RicardoSung/Apple_Sugar_Detector/PCB/v3/FPGA_CCD/allegro/test.png

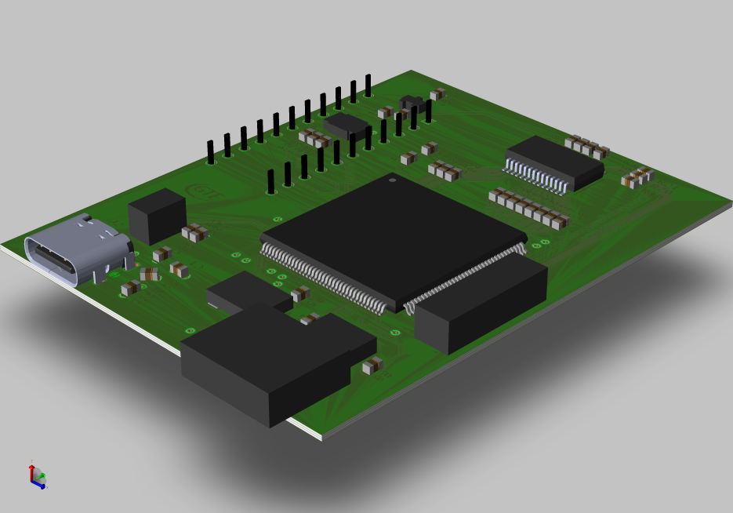
PCB/v3/FPGA_CCD/allegro/test.png
