RicardoSung/Apple_Sugar_Detector/Verilog/v1/UART.v

`timescale 1ns / 1ps
//////////////////////////////////////////////////////////////////////////////////
// Company: 
// Engineer: 
// 
// Create Date:    12:24:14 06/28/2021 
// Design Name: 
// Module Name:    UART 
// Project Name: 
// Target Devices: 
// Tool versions: 
// Description: 
//
// Dependencies: 
//
// Revision: 
// Revision 0.01 - File Created
// Additional Comments: 
//
//////////////////////////////////////////////////////////////////////////////////
module UART(
    );


endmodule
