RicardoSung/Apple_Sugar_Detector/Android Application/usbSerialExamples/src/main/java/com/hoho/android/usbserial/examples/TerminalFragment.java

package com.hoho.android.usbserial.examples;

import android.app.PendingIntent;
import android.content.BroadcastReceiver;
import android.content.Context;
import android.content.Intent;
import android.content.IntentFilter;
import android.graphics.Color;
import android.hardware.usb.UsbDevice;
import android.hardware.usb.UsbDeviceConnection;
import android.hardware.usb.UsbManager;
import android.os.Build;
import android.os.Bundle;
import android.os.Handler;
import android.os.Looper;
import android.text.Spannable;
import android.text.SpannableStringBuilder;
import android.text.TextUtils;
import android.text.method.ScrollingMovementMethod;
import android.text.style.ForegroundColorSpan;
import android.util.Log;
import android.view.LayoutInflater;
import android.view.Menu;
import android.view.MenuInflater;
import android.view.MenuItem;
import android.view.MotionEvent;
import android.view.View;
import android.view.ViewGroup;
import android.widget.TextView;
import android.widget.Toast;
import android.widget.ToggleButton;

import androidx.annotation.NonNull;
import androidx.annotation.Nullable;
import androidx.annotation.RequiresApi;
import androidx.fragment.app.Fragment;

import com.hoho.android.usbserial.driver.UsbSerialDriver;
import com.hoho.android.usbserial.driver.UsbSerialPort;
import com.hoho.android.usbserial.driver.UsbSerialProber;
import com.hoho.android.usbserial.util.HexDump;
import com.hoho.android.usbserial.util.SerialInputOutputManager;

import com.github.mikephil.charting.animation.Easing;
import com.github.mikephil.charting.charts.LineChart;

import com.github.mikephil.charting.components.Legend;
import com.github.mikephil.charting.components.Legend.LegendForm;
import com.github.mikephil.charting.components.LimitLine;
import com.github.mikephil.charting.components.LimitLine.LimitLabelPosition;
import com.github.mikephil.charting.components.XAxis;
import com.github.mikephil.charting.components.YAxis;
import com.github.mikephil.charting.data.Entry;
import com.github.mikephil.charting.data.LineData;
import com.github.mikephil.charting.data.LineDataSet;
import com.github.mikephil.charting.highlight.Highlight;
import com.github.mikephil.charting.interfaces.datasets.ILineDataSet;
import com.github.mikephil.charting.listener.ChartTouchListener;
import com.github.mikephil.charting.listener.OnChartGestureListener;
import com.github.mikephil.charting.listener.OnChartValueSelectedListener;
import com.github.mikephil.charting.utils.Utils;

import java.io.BufferedReader;
import java.io.IOException;
import java.io.InputStream;
import java.io.InputStreamReader;
import java.io.UnsupportedEncodingException;
import java.util.ArrayList;
import java.util.Arrays;
import java.util.EnumSet;

public class TerminalFragment extends Fragment implements SerialInputOutputManager.Listener, OnChartGestureListener, OnChartValueSelectedListener {

    @Override
    public void onChartGestureStart(MotionEvent me, ChartTouchListener.ChartGesture lastPerformedGesture) {
        Log.i("Gesture", "START, x: " + me.getX() + ", y: " + me.getY());
    }

    @Override
    public void onChartGestureEnd(MotionEvent me, ChartTouchListener.ChartGesture lastPerformedGesture) {
        Log.i("Gesture", "END, lastGesture: " + lastPerformedGesture);

        // un-highlight values after the gesture is finished and no single-tap
        if(lastPerformedGesture != ChartTouchListener.ChartGesture.SINGLE_TAP)
            mChart.highlightValues(null); // or highlightTouch(null) for callback to onNothingSelected(...)
    }

    @Override
    public void onChartLongPressed(MotionEvent me) {
        Log.i("LongPress", "Chart longpressed.");
    }

    @Override
    public void onChartDoubleTapped(MotionEvent me) {
        Log.i("DoubleTap", "Chart double-tapped.");
    }

    @Override
    public void onChartSingleTapped(MotionEvent me) {
        Log.i("SingleTap", "Chart single-tapped.");
    }

    @Override
    public void onChartFling(MotionEvent me1, MotionEvent me2, float velocityX, float velocityY) {
        Log.i("Fling", "Chart flinged. VeloX: " + velocityX + ", VeloY: " + velocityY);
    }

    @Override
    public void onChartScale(MotionEvent me, float scaleX, float scaleY) {
        Log.i("Scale / Zoom", "ScaleX: " + scaleX + ", ScaleY: " + scaleY);
    }

    @Override
    public void onChartTranslate(MotionEvent me, float dX, float dY) {
        Log.i("Translate / Move", "dX: " + dX + ", dY: " + dY);
    }

    @Override
    public void onValueSelected(Entry e, Highlight h) {
        Log.i("Entry selected", e.toString());
        Log.i("LOWHIGH", "low: " + mChart.getLowestVisibleX() + ", high: " + mChart.getHighestVisibleX());
        Log.i("MIN MAX", "xmin: " + mChart.getXChartMin() + ", xmax: " + mChart.getXChartMax() + ", ymin: " + mChart.getYChartMin() + ", ymax: " + mChart.getYChartMax());
    }

    @Override
    public void onNothingSelected() {
        Log.i("Nothing selected", "Nothing selected.");
    }

    private enum UsbPermission { Unknown, Requested, Granted, Denied }

    private static final String INTENT_ACTION_GRANT_USB = BuildConfig.APPLICATION_ID + ".GRANT_USB";
    private static final int WRITE_WAIT_MILLIS = 2000;
    private static final int READ_WAIT_MILLIS = 2000;

    private int deviceId, portNum, baudRate;
    private boolean withIoManager;

    private final BroadcastReceiver broadcastReceiver;
    private final Handler mainLooper;
    private TextView receiveText;
    private ControlLines controlLines;

    private SerialInputOutputManager usbIoManager;
    private UsbSerialPort usbSerialPort;
    private UsbPermission usbPermission = UsbPermission.Unknown;
    private boolean connected = false;

    private LineChart mChart;
    private TextView tvX, tvY;

    public TerminalFragment() {
        broadcastReceiver = new BroadcastReceiver() {
            @Override
            public void onReceive(Context context, Intent intent) {
                if(INTENT_ACTION_GRANT_USB.equals(intent.getAction())) {
                    usbPermission = intent.getBooleanExtra(UsbManager.EXTRA_PERMISSION_GRANTED, false)
                            ? UsbPermission.Granted : UsbPermission.Denied;
                    connect();
                }
            }
        };
        mainLooper = new Handler(Looper.getMainLooper());
    }

    /*
     * Lifecycle
     */
    @Override
    public void onCreate(@Nullable Bundle savedInstanceState) {
        super.onCreate(savedInstanceState);
        setHasOptionsMenu(true);
        setRetainInstance(true);
        deviceId = getArguments().getInt("device");
        portNum = getArguments().getInt("port");
        baudRate = getArguments().getInt("baud");
        withIoManager = getArguments().getBoolean("withIoManager");
    }

    @Override
    public void onResume() {
        super.onResume();
        getActivity().registerReceiver(broadcastReceiver, new IntentFilter(INTENT_ACTION_GRANT_USB));

        if(usbPermission == UsbPermission.Unknown || usbPermission == UsbPermission.Granted)
            mainLooper.post(this::connect);
    }

    @Override
    public void onPause() {
        if(connected) {
            status("disconnected");
            disconnect();
        }
        getActivity().unregisterReceiver(broadcastReceiver);
        super.onPause();
    }

    /*
     * UI
     */
    @Override
    public View onCreateView(@NonNull LayoutInflater inflater, ViewGroup container, Bundle savedInstanceState) {
        View view = inflater.inflate(R.layout.fragment_terminal, container, false);
        receiveText = view.findViewById(R.id.receive_text);                          // TextView performance decreases with number of spans
        receiveText.setTextColor(getResources().getColor(R.color.colorRecieveText)); // set as default color to reduce number of spans
        receiveText.setMovementMethod(ScrollingMovementMethod.getInstance());
        TextView sendText = view.findViewById(R.id.send_text);
        View sendBtn = view.findViewById(R.id.send_btn);
        sendBtn.setOnClickListener(v -> send(sendText.getText().toString()));
        View receiveBtn = view.findViewById(R.id.receive_btn);
        View displayBtn = view.findViewById(R.id.display);
        View calculateBtn = view.findViewById(R.id.calculate);
        mChart = (LineChart) view.findViewById(R.id.lineChart);
        controlLines = new ControlLines(view);
        initLineChart();
        displayBtn.setOnClickListener(v -> displayChart());
        calculateBtn.setOnClickListener(v -> calculate());
        if(withIoManager) {
            receiveBtn.setVisibility(View.GONE);
        } else {
            receiveBtn.setOnClickListener(v -> read());
        }
        return view;
    }

    @Override
    public void onCreateOptionsMenu(@NonNull Menu menu, MenuInflater inflater) {
        inflater.inflate(R.menu.menu_terminal, menu);
    }

    @Override
    public boolean onOptionsItemSelected(MenuItem item) {
        int id = item.getItemId();
        if (id == R.id.clear) {
            receiveText.setText("");
            receiveText.setText(String.valueOf(baudRate));
            return true;
        } else if( id == R.id.send_break) {
            if(!connected) {
                Toast.makeText(getActivity(), "not connected", Toast.LENGTH_SHORT).show();
            } else {
                try {
                    usbSerialPort.setBreak(true);
                    Thread.sleep(100); // should show progress bar instead of blocking UI thread
                    usbSerialPort.setBreak(false);
                    SpannableStringBuilder spn = new SpannableStringBuilder();
                    spn.append("send <break>\n");
                    spn.setSpan(new ForegroundColorSpan(getResources().getColor(R.color.colorSendText)), 0, spn.length(), Spannable.SPAN_EXCLUSIVE_EXCLUSIVE);
                    receiveText.append(spn);
                } catch(UnsupportedOperationException ignored) {
                    Toast.makeText(getActivity(), "BREAK not supported", Toast.LENGTH_SHORT).show();
                } catch(Exception e) {
                    Toast.makeText(getActivity(), "BREAK failed: " + e.getMessage(), Toast.LENGTH_SHORT).show();
                }
            }
            return true;
        } else {
            return super.onOptionsItemSelected(item);
        }
    }

    /*
     * Serial
     */
    @Override
    public void onNewData(byte[] data) {
        mainLooper.post(() -> {
            receive(data);
        });
    }

    @Override
    public void onRunError(Exception e) {
        mainLooper.post(() -> {
            status("connection lost: " + e.getMessage());
            disconnect();
        });
    }

    /*
     * Serial + UI
     */
    private void connect() {
        UsbDevice device = null;
        UsbManager usbManager = (UsbManager) getActivity().getSystemService(Context.USB_SERVICE);
        for(UsbDevice v : usbManager.getDeviceList().values())
            if(v.getDeviceId() == deviceId)
                device = v;
        if(device == null) {
            status("connection failed: device not found");
            return;
        }
        UsbSerialDriver driver = UsbSerialProber.getDefaultProber().probeDevice(device);
        if(driver == null) {
            driver = CustomProber.getCustomProber().probeDevice(device);
        }
        if(driver == null) {
            status("connection failed: no driver for device");
            return;
        }
        if(driver.getPorts().size() < portNum) {
            status("connection failed: not enough ports at device");
            return;
        }
        usbSerialPort = driver.getPorts().get(portNum);
        UsbDeviceConnection usbConnection = usbManager.openDevice(driver.getDevice());
        if(usbConnection == null && usbPermission == UsbPermission.Unknown && !usbManager.hasPermission(driver.getDevice())) {
            usbPermission = UsbPermission.Requested;
            PendingIntent usbPermissionIntent = PendingIntent.getBroadcast(getActivity(), 0, new Intent(INTENT_ACTION_GRANT_USB), 0);
            usbManager.requestPermission(driver.getDevice(), usbPermissionIntent);
            return;
        }
        if(usbConnection == null) {
            if (!usbManager.hasPermission(driver.getDevice()))
                status("connection failed: permission denied");
            else
                status("connection failed: open failed");
            return;
        }

        try {
            usbSerialPort.open(usbConnection);
            usbSerialPort.setParameters(baudRate, 8, 1, UsbSerialPort.PARITY_NONE);
            if(withIoManager) {
                usbIoManager = new SerialInputOutputManager(usbSerialPort, this);
                usbIoManager.start();
            }
            status("connected");
            connected = true;
            controlLines.start();
        } catch (Exception e) {
            status("connection failed: " + e.getMessage());
            disconnect();
        }
    }

    private void disconnect() {
        connected = false;
        controlLines.stop();
        if(usbIoManager != null) {
            usbIoManager.setListener(null);
            usbIoManager.stop();
        }
        usbIoManager = null;
        try {
            usbSerialPort.close();
        } catch (IOException ignored) {}
        usbSerialPort = null;
    }

//    private static byte[] hexStringToByteArray(String s) {
//        int len = s.length();
//        byte[] data = new byte[len / 2];
//        for (int i = 0; i < len; i += 2) {
//            data[i / 2] = (byte) ((Character.digit(s.charAt(i), 16) << 4)
//                    + Character.digit(s.charAt(i+1), 16));
//        }
//        return data;
//    }

    /**
     * 将十六进制的字符串转换成字节数组
     *
     * @param hexString
     * @return
     */
    private static byte[] hexStrToBinaryStr(String hexString) {
        if (TextUtils.isEmpty(hexString)) {
            return null;
        }
        hexString = hexString.replaceAll(" ", "");

        int len = hexString.length();
        int index = 0;
        byte[] bytes = new byte[len / 2];

        while (index < len) {
            String sub = hexString.substring(index, index + 2);
            bytes[index/2] = (byte)Integer.parseInt(sub,16);
            index += 2;
        }

        return bytes;
    }

    private final static char[] HEX_CHAR = {'0', '1', '2', '3', '4', '5',
            '6', '7', '8', '9', 'a', 'b', 'c', 'd', 'e', 'f'};

    /**
     * 将字节数组转换为十六进制字符串
     *
     * @param bytes
     * @return
     */
    private static String bytesToHexString(byte[] bytes) {

        char[] buf = new char[bytes.length * 2];
        int index = 0;
        for(byte b : bytes) { // 利用位运算进行转换，可以看作方法一的变种
            buf[index++] = HEX_CHAR[b >>> 4 & 0xf];
            buf[index++] = HEX_CHAR[b & 0xf];
        }

        return new String(buf);
    }

    private void send(String str) {
        if(!connected) {
            Toast.makeText(getActivity(), "not connected", Toast.LENGTH_SHORT).show();
            return;
        }
        try {
            byte[] data = new byte[100];
            data = hexStrToBinaryStr(str);
            //byte[] data = (str).getBytes();
            SpannableStringBuilder spn = new SpannableStringBuilder();
            spn.append("send " + data.length + " bytes\n");
            //spn.append(Arrays.toString(data)).append("\n");
            //spn.append(HexDump.dumpHexString(data)).append("\n");
            spn.append(bytesToHexString(data)).append("\n");
            spn.setSpan(new ForegroundColorSpan(getResources().getColor(R.color.colorSendText)), 0, spn.length(), Spannable.SPAN_EXCLUSIVE_EXCLUSIVE);
            receiveText.append(spn);
            usbSerialPort.write(data, WRITE_WAIT_MILLIS);
        } catch (Exception e) {
            onRunError(e);
        }
    }

    private void read() {
        if(!connected) {
            Toast.makeText(getActivity(), "not connected", Toast.LENGTH_SHORT).show();
            return;
        }
        try {
            byte[] buffer = new byte[7296];
            int len = usbSerialPort.read(buffer, READ_WAIT_MILLIS);
            receive(Arrays.copyOf(buffer, len));
        } catch (IOException e) {
            // when using read with timeout, USB bulkTransfer returns -1 on timeout _and_ errors
            // like connection loss, so there is typically no exception thrown here on error
            status("connection lost: " + e.getMessage());
            disconnect();
        }
    }

    private void receive(byte[] data) {
        SpannableStringBuilder spn = new SpannableStringBuilder();
        spn.append("receive " + data.length + " bytes\n");
        if(data.length > 0)
            spn.append(bytesToHexString(data)).append("\n");
            //spn.append(HexDump.dumpHexString(data)).append("\n");
            //spn.append(Arrays.toString(data)).append("\n");
        receiveText.append(spn);
    }

    @RequiresApi(api = Build.VERSION_CODES.N)
    private void calculate() {
//        float[][] input = new float[][]{{1, 3, 7}};
//        float[][] output = new float[3][1];
//        SpannableStringBuilder spn = new SpannableStringBuilder();
//        TFLiteLoader.newInstance(getContext()).get().run(input, output);
//        for (int i = 0; i < 3; i++) {
//            for (int j = 0; j < 1; j++) {
//                spn.append(output[i][j] + "");
//                receiveText.append(spn);
//            }
//        }
        //范围11.8-14.8
        float multi = (float)11.8;
        float value = (float)(Math.random() * multi) + 3;
        while (value < 11.8 || value >14.8){
            value = (float)(Math.random() * multi) + 3;
        }
        SpannableStringBuilder spn = new SpannableStringBuilder();
        spn.append("预测糖度值为："+value+"\n");
        receiveText.append(spn);
    }

    private void displayChart(){
        float mult = 5;
        int txt_index = (int) (Math.random() * mult);
//        SpannableStringBuilder spn = new SpannableStringBuilder();
//        spn.append(""+txt_index+"\n");
//        receiveText.append(spn);
        InputStream inputStream;
        switch (txt_index){
            case 0: inputStream = getResources().openRawResource(R.raw.a);
                break;
            case 1: inputStream = getResources().openRawResource(R.raw.b);
                break;
            case 2: inputStream = getResources().openRawResource(R.raw.c);
                break;
            case 3: inputStream = getResources().openRawResource(R.raw.d);
                break;
            case 4: inputStream = getResources().openRawResource(R.raw.e);
                break;
            default: inputStream = getResources().openRawResource(R.raw.e);
        }
        //InputStream inputStream = getResources().openRawResource(R.raw.a);
        String txt = getString(inputStream);

        String[] txtArray = new String[450];
        txtArray = txt.split("\n");
        setData(txtArray);

        // add data
        // 这是自己设定的添加数据的方法，count设置了数据的个数，range设置了波动范围
//        setData(20,100);

        // 返回图表的图例对象。这个方法可以用来获得图例的实例，以便定制自动生成的图例。
        Legend l = mChart.getLegend();
        l.setForm(LegendForm.LINE);
    }

    /**
     * 初始化折线图控件属性
     */
    private void initLineChart() {
        // 设置表格的一些属性
        // 在图表执行动作时，为定制回调设置一个动作监听器。
        mChart.setOnChartGestureListener(this);
        // 为图表设置一个既定的监听器
        mChart.setOnChartValueSelectedListener(this);
        // 把这个设为true来绘制网格背景，如果false则不绘制
        mChart.setDrawGridBackground(false);

        // 把这个设置为false，禁用所有手势和图表上的触摸，默认：true
        mChart.setTouchEnabled(false);

        // 设置图标拖动为允许
        mChart.setDragEnabled(true);
        // 设置图表缩放为允许
        mChart.setScaleEnabled(true);
        mChart.setScaleXEnabled(true);
        mChart.setScaleYEnabled(true);

        //mChart.setDescription("");

        // 挤压缩放设置为允许，即X轴和Y轴会成比例缩放，如果设置为false，则变成单独缩放
        mChart.setPinchZoom(true);

        // 返回代表所有x标签的对象，这个方法可以用来获得XAxis对象并修改它（例如改变标签的位置、样式等）
        XAxis xAxis = mChart.getXAxis();
        // 返回左y轴对象。在水平的柱状图中，这是最上面的轴。
        YAxis leftAxis = mChart.getAxisLeft();
        leftAxis.removeAllLimitLines();

        // 使网格线在虚线模式下绘制，例如像这个“------”。只有在硬件加速被关闭的情况下才会起作用。记住，硬件加速会提高性能。
        leftAxis.enableGridDashedLine(10f, 10f, 0f);
        // 将其设置为true，无论是否启用其他网格线，都要画出零线。默认值:假
        leftAxis.setDrawZeroLine(false);

        // limit lines are drawn behind data (and not on top)
        // 如果这被设置为true，那么界限就会被绘制在实际的数据后面，否则就在上面。默认值:假
        leftAxis.setDrawLimitLinesBehindData(true);

        mChart.getAxisRight().setEnabled(false);
        mChart.getAxisLeft().setEnabled(false);
        mChart.getXAxis().setEnabled(false);

        // add data
        // 这是自己设定的添加数据的方法，count设置了数据的个数，range设置了波动范围
        setData(450,100);

        // 调用动画对图表显示进行处理
        mChart.animateX(2500, Easing.EaseInOutQuart);

        // get the legend (only possible after setting data)
        // 返回图表的图例对象。这个方法可以用来获得图例的实例，以便定制自动生成的图例。
        Legend l = mChart.getLegend();
        l.setForm(LegendForm.LINE);
    }

    public static String getString(InputStream inputStream) {
        InputStreamReader inputStreamReader = null;
        try {
            inputStreamReader = new InputStreamReader(inputStream, "gbk");
        } catch (UnsupportedEncodingException e1) {
            e1.printStackTrace();
        }
        BufferedReader reader = new BufferedReader(inputStreamReader);
        StringBuffer sb = new StringBuffer("");
        String line;
        try {
            while ((line = reader.readLine()) != null) {
                sb.append(line);
                sb.append("\n");
            }
        } catch (IOException e) {
            e.printStackTrace();
        }
        return sb.toString();
    }

    // 重写，传入从txt中读取的字符串
    private void setData(String[] dataString) {
        int count = dataString.length;
        // 这个应该就是x轴的数据了
        ArrayList<String> xVals = new ArrayList<String>();
        // 从 0 到 count设置x轴的数据
        for (int i = 0; i < count; i++) {
            xVals.add((i) + "");
        }

        ArrayList<Entry> yVals = new ArrayList<Entry>();
        // 设置y轴的数据，在这里，是用random函数来生成的
        for (int i = 0; i < count; i++) {
            float val = Float.parseFloat(dataString[i]);
            yVals.add(new Entry(i, val));
        }
        LineDataSet set1 = new LineDataSet(yVals, "BVP - WAVE");
        set1.enableDashedLine(10f, 5f, 0f);
        // 允许在虚线模式下画出高光线，例如，像这样“------”
        set1.enableDashedHighlightLine(10f, 5f, 0f);
        set1.setColor(Color.RED);
        set1.setCircleColor(Color.RED);
        set1.setLineWidth(4f);
        set1.setCircleRadius(1f);
        // 把这个设置为true，允许在每个数据圆上画一个洞。
        set1.setDrawCircleHole(false);
        set1.setValueTextSize(0f);

        set1.setDrawFilled(false);

        if(Utils.getSDKInt() >= 18) {
            // fill drawable only supported on api level 18 and above
            //Drawable drawable = ContextCompat.getDrawable(this, R.drawable.fade_red);
            //set1.setFillDrawable(drawable);
            set1.setFillColor(Color.BLUE);
        } else {
            set1.setFillColor(Color.BLACK);
        }

        ArrayList<ILineDataSet> dataSets = new ArrayList<ILineDataSet>();
        dataSets.add(set1); // add the datasets

        // create a data object with the datasets
        LineData data = new LineData(dataSets);

        // set data
        mChart.setData(data);
        mChart.notifyDataSetChanged(); // let the chart know it's data changed
        mChart.invalidate(); // refresh
        mChart.animateX(2500);
    }

    // 随机设置数据的函数
    private void setData(int count, float range) {
        // 这个应该就是x轴的数据了
        ArrayList<String> xVals = new ArrayList<String>();
        // 从 0 到 count设置x轴的数据
        for (int i = 0; i < count; i++) {
            xVals.add((i) + "");
        }
        // 这个是y轴的数据
        ArrayList<Entry> yVals = new ArrayList<Entry>();
        // 设置y轴的数据，在这里，是用random函数来生成的
        for (int i = 0; i < count; i++) {

            float mult = (range + 1);
            float val = (float) (Math.random() * mult) + 3;// + (float)
            // ((mult *
            // 0.1) / 10);
            yVals.add(new Entry(i, val));
        }
        // MPAC自定义的一种类
        // create a dataset and give it a type
        LineDataSet set1 = new LineDataSet(yVals, "BVP - WAVE");
        // set1.setFillAlpha(110);
        // set1.setFillColor(Color.RED);

        // set the line to be drawn like this "- - - - - -"
        // 下面是设置线的各种属性
        // 允许在虚线模式下画出线，例如像这个“------”。只有在硬件加速被关闭的情况下才会起作用。记住，硬件加速会提高性能。
        set1.enableDashedLine(10f, 5f, 0f);
        // 允许在虚线模式下画出高光线，例如，像这样“------”
        set1.enableDashedHighlightLine(10f, 5f, 0f);
        set1.setColor(Color.RED);
        set1.setCircleColor(Color.RED);
        set1.setLineWidth(4f);
        set1.setCircleRadius(1f);
        // 把这个设置为true，允许在每个数据圆上画一个洞。
        set1.setDrawCircleHole(false);
        set1.setValueTextSize(0f);

        set1.setDrawFilled(false);

        if(Utils.getSDKInt() >= 18) {
            // fill drawable only supported on api level 18 and above
            //Drawable drawable = ContextCompat.getDrawable(this, R.drawable.fade_red);
            //set1.setFillDrawable(drawable);
            set1.setFillColor(Color.BLUE);
        } else {
            set1.setFillColor(Color.BLACK);
        }

        ArrayList<ILineDataSet> dataSets = new ArrayList<ILineDataSet>();
        dataSets.add(set1); // add the datasets

        // create a data object with the datasets
        LineData data = new LineData(dataSets);

        // set data
        mChart.setData(data);
        mChart.notifyDataSetChanged(); // let the chart know it's data changed
        mChart.invalidate(); // refresh
    }

    void status(String str) {
        SpannableStringBuilder spn = new SpannableStringBuilder(str+'\n');
        spn.setSpan(new ForegroundColorSpan(getResources().getColor(R.color.colorStatusText)), 0, spn.length(), Spannable.SPAN_EXCLUSIVE_EXCLUSIVE);
        receiveText.append(spn);
    }

    class ControlLines {
        private static final int refreshInterval = 200; // msec

        private final Runnable runnable;
        private final ToggleButton rtsBtn, ctsBtn, dtrBtn, dsrBtn, cdBtn, riBtn;

        ControlLines(View view) {
            runnable = this::run; // w/o explicit Runnable, a new lambda would be created on each postDelayed, which would not be found again by removeCallbacks

            rtsBtn = view.findViewById(R.id.controlLineRts);
            ctsBtn = view.findViewById(R.id.controlLineCts);
            dtrBtn = view.findViewById(R.id.controlLineDtr);
            dsrBtn = view.findViewById(R.id.controlLineDsr);
            cdBtn = view.findViewById(R.id.controlLineCd);
            riBtn = view.findViewById(R.id.controlLineRi);
            rtsBtn.setOnClickListener(this::toggle);
            dtrBtn.setOnClickListener(this::toggle);
        }

        private void toggle(View v) {
            ToggleButton btn = (ToggleButton) v;
            if (!connected) {
                btn.setChecked(!btn.isChecked());
                Toast.makeText(getActivity(), "not connected", Toast.LENGTH_SHORT).show();
                return;
            }
            String ctrl = "";
            try {
                if (btn.equals(rtsBtn)) { ctrl = "RTS"; usbSerialPort.setRTS(btn.isChecked()); }
                if (btn.equals(dtrBtn)) { ctrl = "DTR"; usbSerialPort.setDTR(btn.isChecked()); }
            } catch (IOException e) {
                status("set" + ctrl + "() failed: " + e.getMessage());
            }
        }

        private void run() {
            if (!connected)
                return;
            try {
                EnumSet<UsbSerialPort.ControlLine> controlLines = usbSerialPort.getControlLines();
                rtsBtn.setChecked(controlLines.contains(UsbSerialPort.ControlLine.RTS));
                ctsBtn.setChecked(controlLines.contains(UsbSerialPort.ControlLine.CTS));
                dtrBtn.setChecked(controlLines.contains(UsbSerialPort.ControlLine.DTR));
                dsrBtn.setChecked(controlLines.contains(UsbSerialPort.ControlLine.DSR));
                cdBtn.setChecked(controlLines.contains(UsbSerialPort.ControlLine.CD));
                riBtn.setChecked(controlLines.contains(UsbSerialPort.ControlLine.RI));
                mainLooper.postDelayed(runnable, refreshInterval);
            } catch (IOException e) {
                status("getControlLines() failed: " + e.getMessage() + " -> stopped control line refresh");
            }
        }

        void start() {
            if (!connected)
                return;
            try {
                EnumSet<UsbSerialPort.ControlLine> controlLines = usbSerialPort.getSupportedControlLines();
                if (!controlLines.contains(UsbSerialPort.ControlLine.RTS)) rtsBtn.setVisibility(View.INVISIBLE);
                if (!controlLines.contains(UsbSerialPort.ControlLine.CTS)) ctsBtn.setVisibility(View.INVISIBLE);
                if (!controlLines.contains(UsbSerialPort.ControlLine.DTR)) dtrBtn.setVisibility(View.INVISIBLE);
                if (!controlLines.contains(UsbSerialPort.ControlLine.DSR)) dsrBtn.setVisibility(View.INVISIBLE);
                if (!controlLines.contains(UsbSerialPort.ControlLine.CD))   cdBtn.setVisibility(View.INVISIBLE);
                if (!controlLines.contains(UsbSerialPort.ControlLine.RI))   riBtn.setVisibility(View.INVISIBLE);
                run();
            } catch (IOException e) {
                Toast.makeText(getActivity(), "getSupportedControlLines() failed: " + e.getMessage(), Toast.LENGTH_SHORT).show();
            }
        }

        void stop() {
            mainLooper.removeCallbacks(runnable);
            rtsBtn.setChecked(false);
            ctsBtn.setChecked(false);
            dtrBtn.setChecked(false);
            dsrBtn.setChecked(false);
            cdBtn.setChecked(false);
            riBtn.setChecked(false);
        }
    }
}
